rbello/FreecomRF433/Photos/image1.JPG

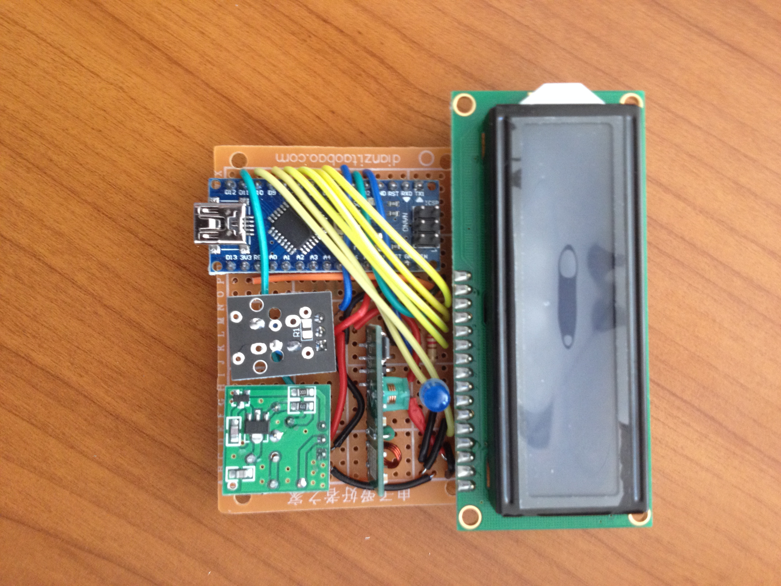
Photos/image1.JPG
