rbello/FreecomRF433/Photos/image2.JPG

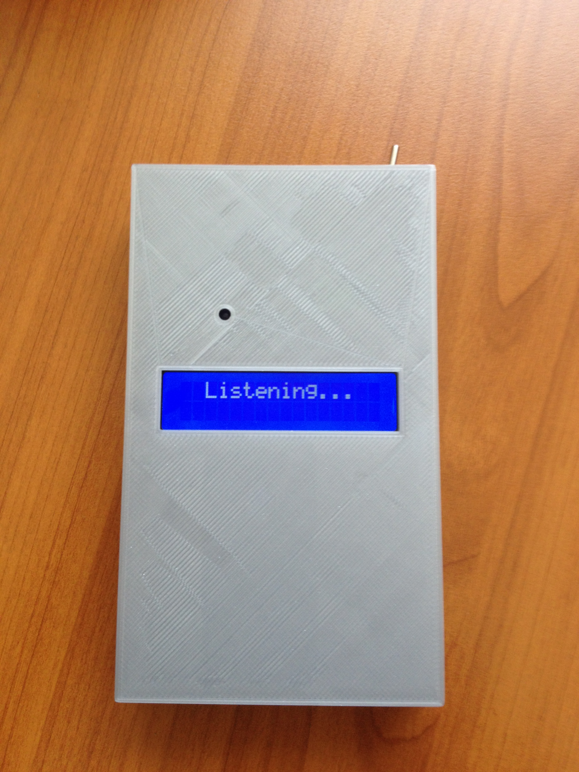
Photos/image2.JPG
