rbello/FreecomRF433/Photos/image3.JPG

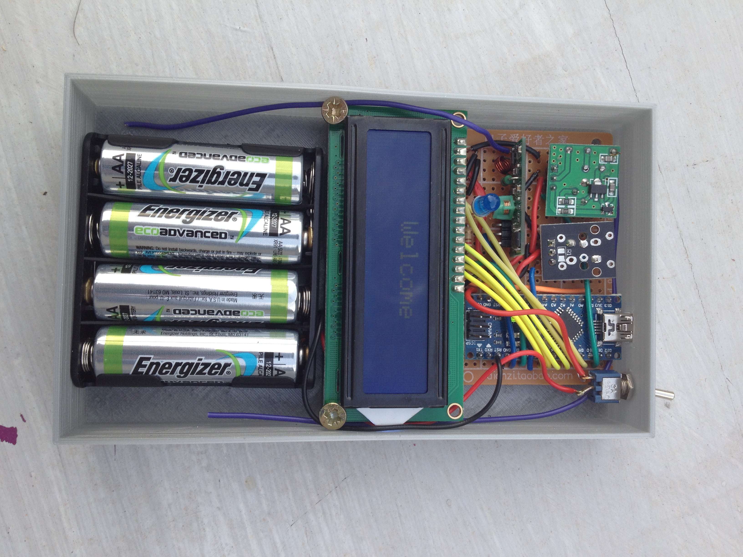
Photos/image3.JPG
